casdata/OP-FM-Shield/Software/OpFM_Shield/midi_voices.h

const uint8_t VOICE1[30]    PROGMEM = { 0x3C, 0x33, 0x5A, 0xB2, 0x50, 0x01, 0x31, 0x00, 0xB1, 0xF5, 0x01, 0x30, 0x41, 0x2E, 0x20, 0x47, 0x52, 0x41, 0x4E, 0x44, 0x20, 0x50, 0x49, 0x41, 0x4E, 0x4F, 0x00, 0x00, 0x00, 0x00 };
const uint8_t VOICE2[30]    PROGMEM = { 0x3C, 0x31, 0x49, 0xF2, 0x53, 0x07, 0x11, 0x03, 0xF1, 0xF5, 0x00, 0x31, 0x42, 0x52, 0x49, 0x47, 0x48, 0x54, 0x20, 0x41, 0x2E, 0x20, 0x50, 0x49, 0x41, 0x4E, 0x4F, 0x00, 0x00, 0x00 };
const uint8_t VOICE3[30]    PROGMEM = { 0x3C, 0x31, 0x95, 0xD1, 0x83, 0x0D, 0x32, 0x03, 0xC1, 0xF5, 0x00, 0x31, 0x45, 0x2E, 0x20, 0x47, 0x52, 0x41, 0x4E, 0x44, 0x20, 0x50, 0x49, 0x41, 0x4E, 0x4F, 0x00, 0x00, 0x00, 0x00 };
const uint8_t VOICE4[30]    PROGMEM = { 0x3C, 0x34, 0x9B, 0xF3, 0x63, 0x01, 0x11, 0x00, 0x92, 0xF5, 0x01, 0x31, 0x48, 0x4F, 0x4E, 0x4B, 0x59, 0x2D, 0x54, 0x4F, 0x4E, 0x4B, 0x00, 0x00, 0x00, 0x00, 0x00, 0x00, 0x00, 0x00 };
const uint8_t VOICE5[30]    PROGMEM = { 0x3C, 0x27, 0x28, 0xF8, 0xB7, 0x01, 0x91, 0x00, 0xF1, 0xF9, 0x00, 0x32, 0x45, 0x2E, 0x20, 0x50, 0x49, 0x41, 0x4E, 0x4F, 0x20, 0x31, 0x00, 0x00, 0x00, 0x00, 0x00, 0x00, 0x00, 0x00 };
const uint8_t VOICE6[30]    PROGMEM = { 0x3C, 0x1A, 0x2D, 0xF3, 0xEE, 0x01, 0x11, 0x00, 0xF1, 0xF5, 0x00, 0x31, 0x45, 0x2E, 0x20, 0x50, 0x49, 0x41, 0x4E, 0x4F, 0x20, 0x32, 0x00, 0x00, 0x00, 0x00, 0x00, 0x00, 0x00, 0x00 };
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

//const uint8_t VOICE129[41]  PROGMEM = { 0x78, 0x11, 0x3F, 0xF1, 0x05, 0x00, 0x33, 0x6A, 0xE2, 0x05, 0x04, 0x30, 0x11, 0x3F, 0xF1, 0x05, 0x00, 0x33, 0xF4, 0xC2, 0x05, 0x00, 0x31, 0x52, 0x4F, 0x43, 0x4B, 0x20, 0x48, 0x45, 0x41, 0x56, 0x59, 0x20, 0x4F, 0x56, 0x4D, 0x00, 0x00, 0x00, 0x00 };
