casdata/OP-FM-Shield/Software/OpFM_Shield/midi_drums.h

//const uint8_t VOICE1[30]    PROGMEM =               { 0x3C, 0x33, 0x5A, 0xB2, 0x50, 0x01, 0x31, 0x00, 0xB1, 0xF5, 0x01, 0x30, 0x41, 0x2E, 0x20, 0x47, 0x52, 0x41, 0x4E, 0x44, 0x20, 0x50, 0x49, 0x41, 0x4E, 0x4F, 0x00, 0x00, 0x00, 0x00 };
//const unsigned char INSTRUMENT_PIANO1[12]   PROGMEM { 0x00, 0x33, 0x5A, 0xB2, 0x50, 0x01, 0x00, 0x31, 0x00, 0xB1, 0xF5, 0x01 };

const uint8_t DRUMINS_BASS_DR1[30]  PROGMEM = { 0x3C, 0x01, 0x07, 0xFA, 0xFD, 0x05, 0x01, 0x00, 0xF6, 0x47, 0x00, 0x30, 0x42, 0x41, 0x53, 0x53, 0x20, 0x44, 0x52, 0x55, 0x4D, 0x20, 0x31, 0x00, 0x00, 0x00, 0x00, 0x00, 0x00, 0x00 };
const uint8_t DRUMINS_BASS_DR2[30]  PROGMEM = { 0x3C, 0x00, 0x00, 0xF9, 0xF3, 0x05, 0x01, 0x00, 0xF7, 0x8A, 0x00, 0x30, 0x42, 0x41, 0x53, 0x53, 0x20, 0x44, 0x52, 0x55, 0x4D, 0x20, 0x32, 0x00, 0x00, 0x00, 0x00, 0x00, 0x00, 0x00 };
const uint8_t DRUMINS_SNARE[30]     PROGMEM = { 0x3C, 0x24, 0x00, 0xFF, 0x00, 0x0F, 0x02, 0x00, 0xF7, 0xA9, 0x00, 0x30, 0x53, 0x4E, 0x41, 0x52, 0x45, 0x00, 0x00, 0x00, 0x00, 0x00, 0x00, 0x00, 0x00, 0x00, 0x00, 0x00, 0x00, 0x00 };
const uint8_t DRUMINS_TOMTOM[30]    PROGMEM = { 0x3C, 0x06, 0x0A, 0xFA, 0x1F, 0x0C, 0x11, 0x00, 0xF5, 0xF5, 0x00, 0x30, 0x54, 0x4F, 0x4D, 0x2D, 0x54, 0x4F, 0x4D, 0x00, 0x00, 0x00, 0x00, 0x00, 0x00, 0x00, 0x00, 0x00, 0x00, 0x00 };
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
const uint8_t DRUMINS_OP_CUICA[30]  PROGMEM = { 0x3C, 0x25, 0x12, 0x57, 0xF7, 0x01, 0x03, 0x00, 0x78, 0x67, 0x01, 0x31, 0x4F, 0x50, 0x20, 0x43, 0x55, 0x49, 0x43, 0x41, 0x00, 0x00, 0x00, 0x00, 0x00, 0x00, 0x00, 0x00, 0x00, 0x00 };
const uint8_t DRUMINS_MUTED_TRINGLE[30]  PROGMEM = { 0x3C, 0x22, 0x2F, 0xF1, 0xF0, 0x07, 0x27, 0x02, 0xF8, 0xFC, 0x00, 0x30, 0x4D, 0x55, 0x54, 0x45, 0x44, 0x20, 0x54, 0x52, 0x49, 0x41, 0x4E, 0x47, 0x4C, 0x45, 0x00, 0x00, 0x00, 0x00 };
const uint8_t DRUMINS_TRIANGLE[30]  PROGMEM = { 0x3C, 0x26, 0x44, 0xF1, 0xF0, 0x07, 0x27, 0x40, 0xF5, 0xF5, 0x00, 0x30, 0x54, 0x52, 0x49, 0x41, 0x4E, 0x47, 0x4C, 0x45, 0x00, 0x00, 0x00, 0x00, 0x00, 0x00, 0x00, 0x00, 0x00, 0x00 };
const uint8_t DRUMINS_TAIKO[30]     PROGMEM = { 0x3C, 0x02, 0x1D, 0xF5, 0x93, 0x01, 0x00, 0x00, 0xC6, 0x45, 0x00, 0x30, 0x54, 0x41, 0x49, 0x4B, 0x4F, 0x00, 0x00, 0x00, 0x00, 0x00, 0x00, 0x00, 0x00, 0x00, 0x00, 0x00, 0x00, 0x00 };
